jayanttyson/ESP32-Truly-Universal-Remote/Images/5.png

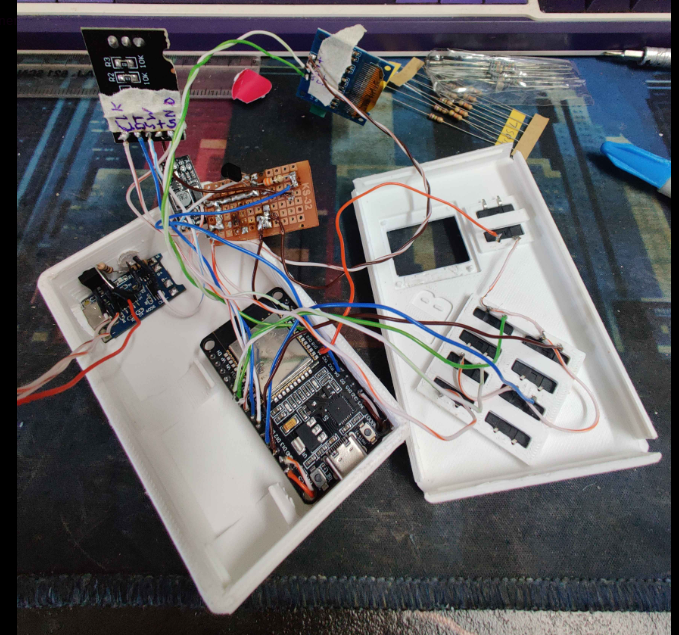
Images/5.png
