jayanttyson/ESP32-Truly-Universal-Remote/Images/6.png

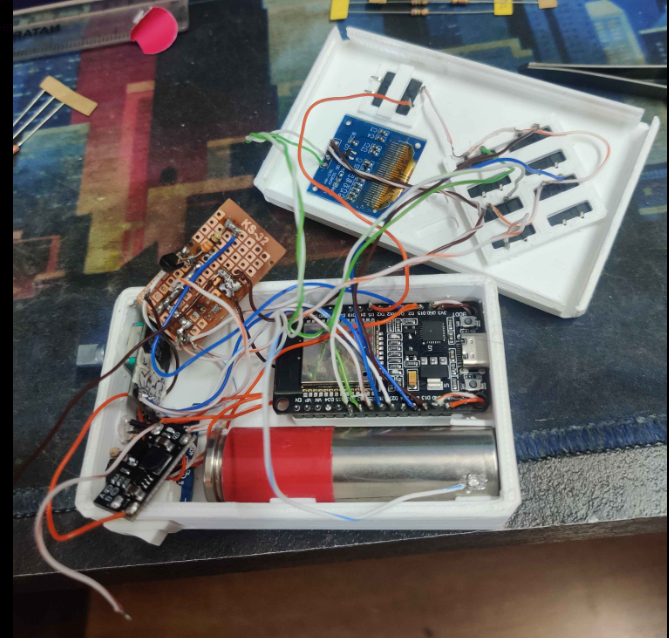
Images/6.png
