jayanttyson/ESP32-Truly-Universal-Remote/Images/8.png

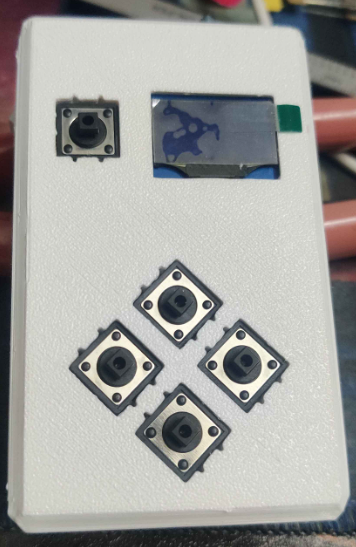
Images/8.png
