jayanttyson/ESP32-Truly-Universal-Remote/Images/11.png

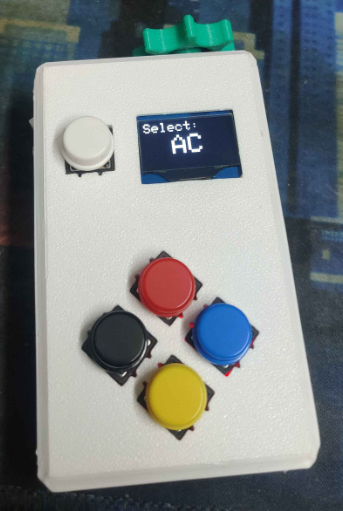
Images/11.png
