jayanttyson/ESP32-Truly-Universal-Remote/Images/12.png

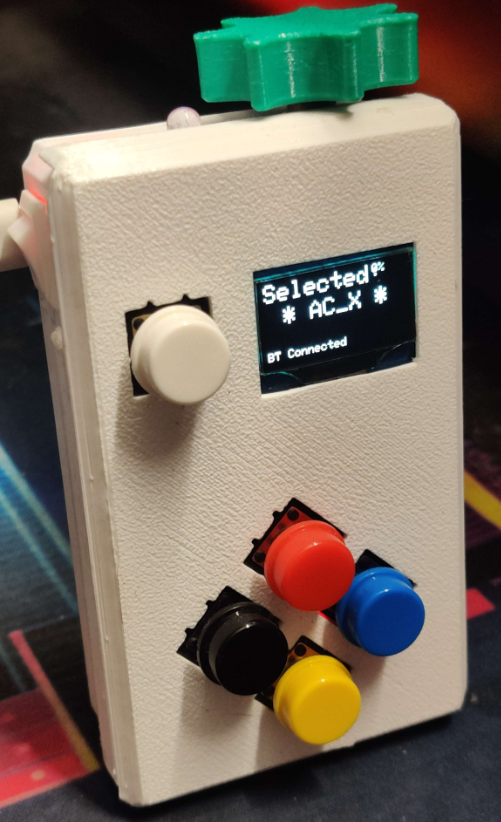
Images/12.png
